Helicon007/Logitech-Wireless-Pedals/pictures/charging_connector_2.jpeg

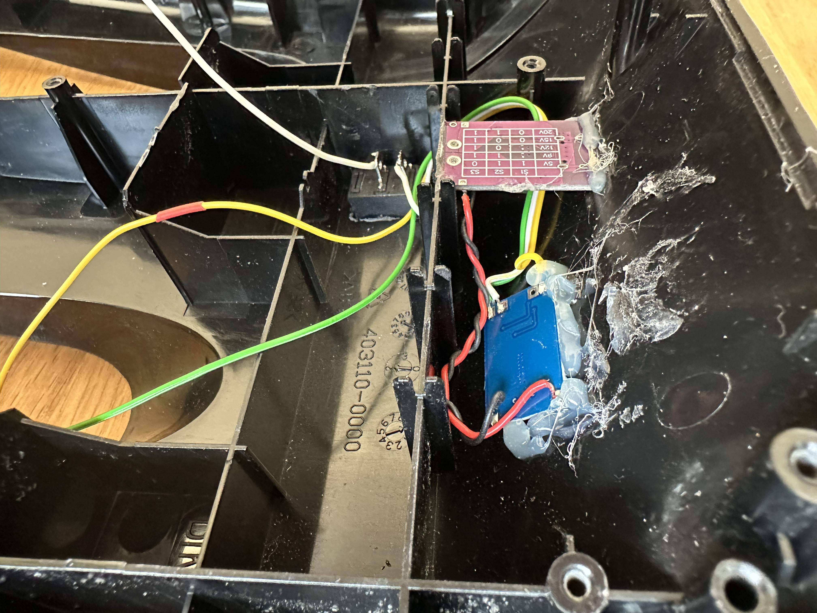
pictures/charging_connector_2.jpeg
