Helicon007/Logitech-Wireless-Pedals/pictures/pedals_case_4.jpeg

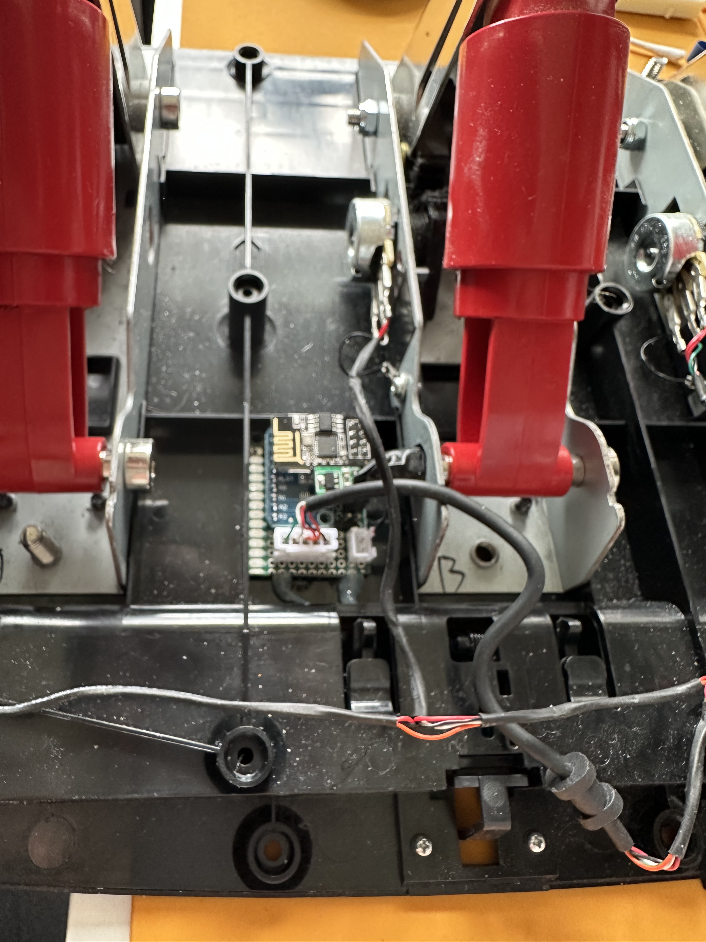
pictures/pedals_case_4.jpeg
