Helicon007/Logitech-Wireless-Pedals/pictures/poti.jpeg

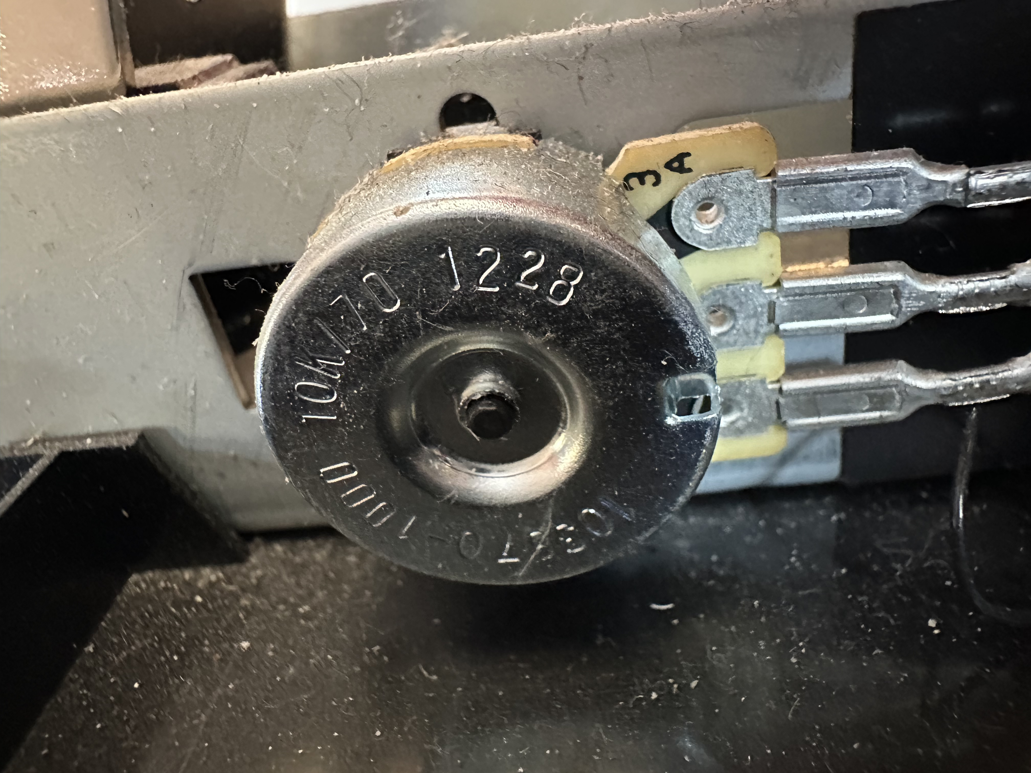
pictures/poti.jpeg
