Helicon007/Logitech-Wireless-Pedals/pictures/sender_board_complete_4.jpeg

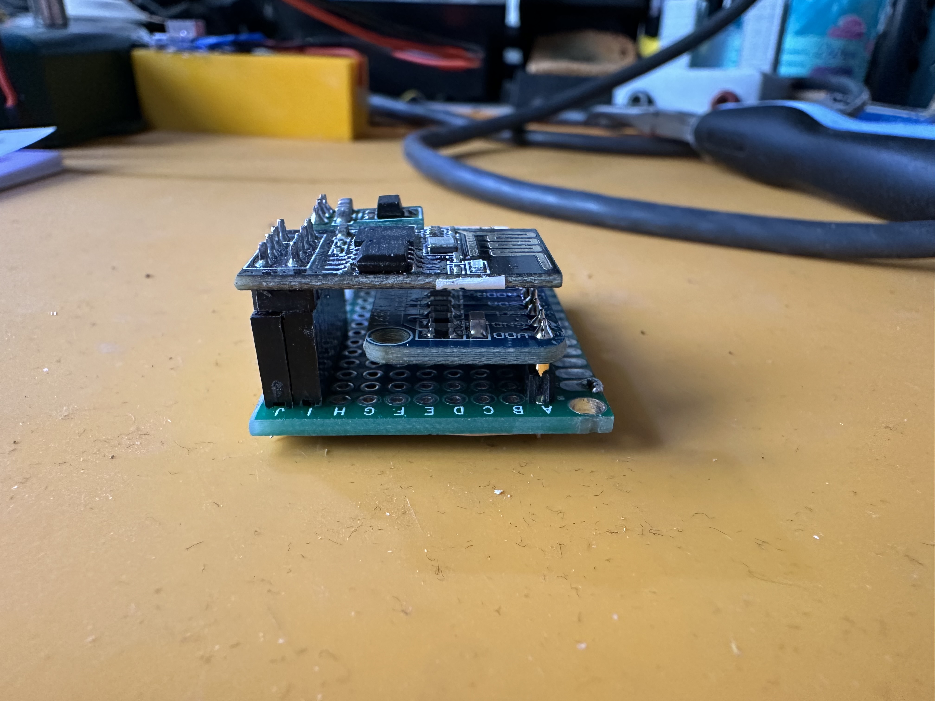
pictures/sender_board_complete_4.jpeg
