Helicon007/Logitech-Wireless-Pedals/pictures/steering_wheel_mainboard_2.jpeg

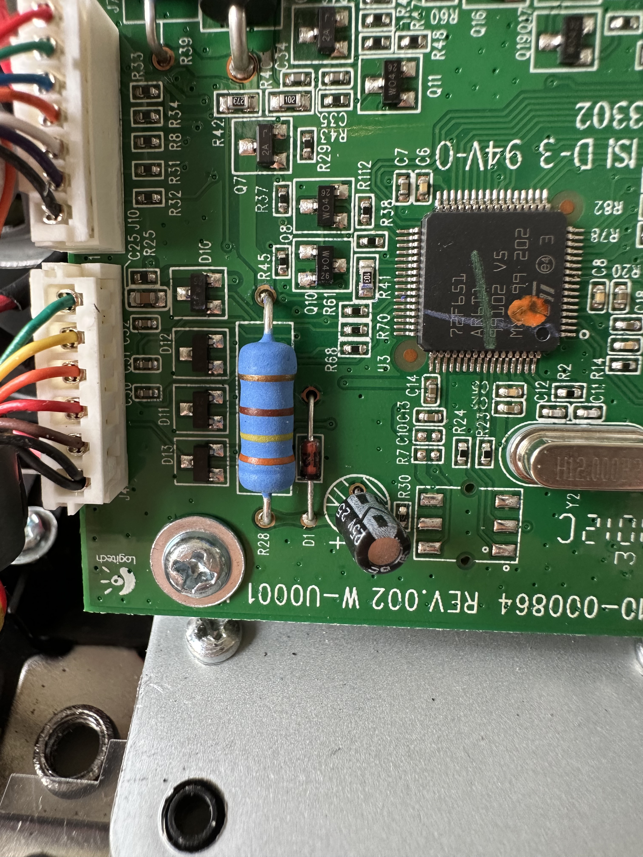
pictures/steering_wheel_mainboard_2.jpeg
