Helicon007/Logitech-Wireless-Pedals/pictures/steering_wheel_subD9.jpeg

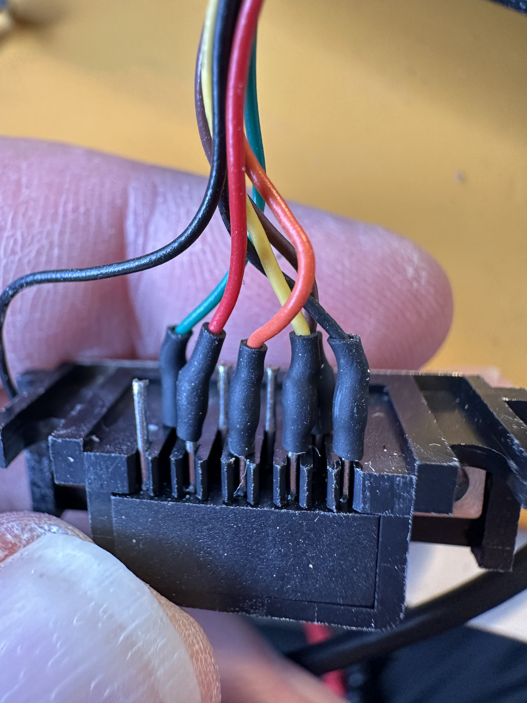
pictures/steering_wheel_subD9.jpeg
