Helicon007/Logitech-Wireless-Pedals/pictures/pedals_case_1.jpeg

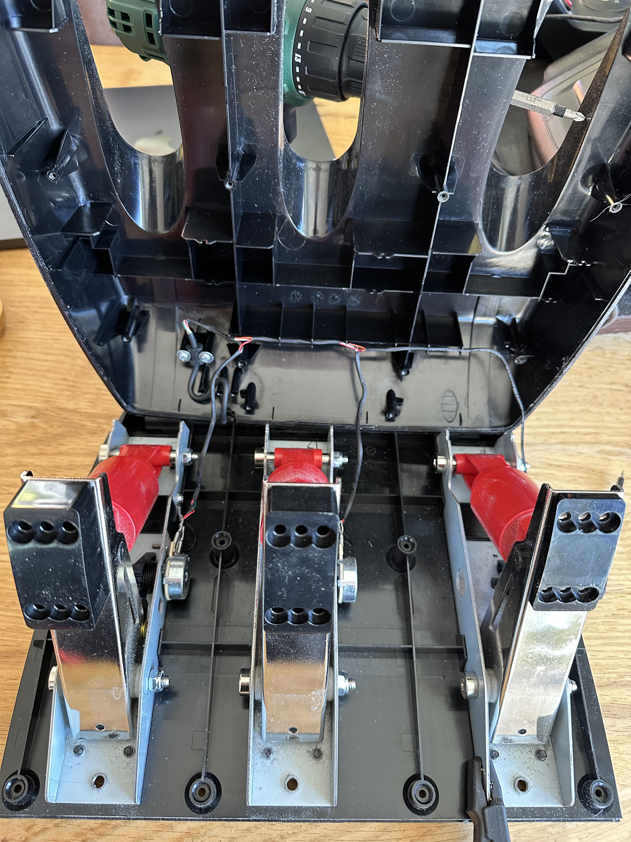
pictures/pedals_case_1.jpeg
