Helicon007/Logitech-Wireless-Pedals/pictures/pedals_case_power_supply_2.jpeg

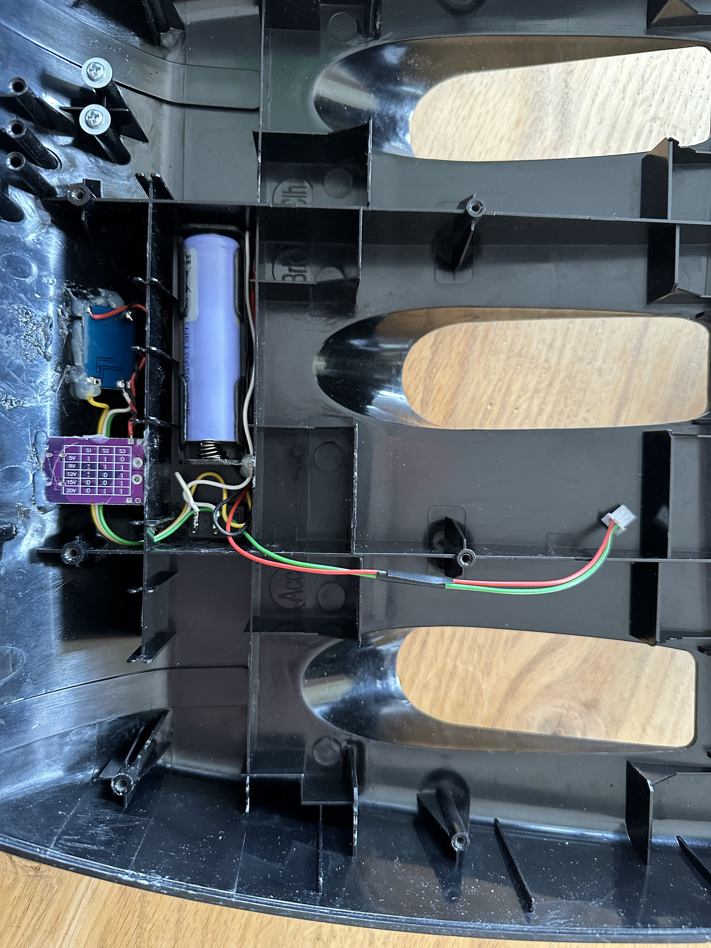
pictures/pedals_case_power_supply_2.jpeg
