Helicon007/Logitech-Wireless-Pedals/pictures/receiver_board_1.jpeg

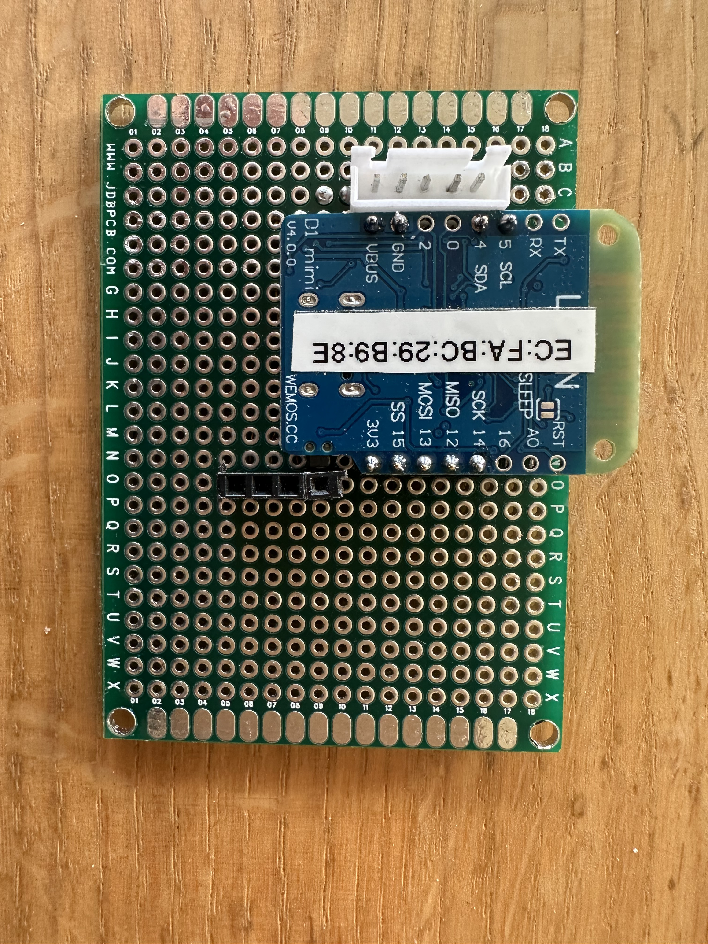
pictures/receiver_board_1.jpeg
